Tasnimanam/A-Low-Cost-3D-Printed-Hand-Exoskeleton-with-Open-Source-Hardware-Licence/Hand Exoskeleton final model's CAD file/Hand ekoskeleton side view.jpg

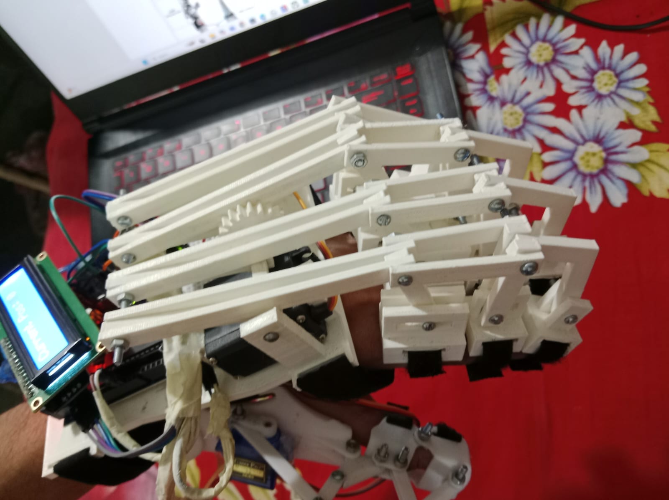
Hand Exoskeleton final model's CAD file/Hand ekoskeleton side view.jpg
