Tasnimanam/A-Low-Cost-3D-Printed-Hand-Exoskeleton-with-Open-Source-Hardware-Licence/Hand Exoskeleton final model's CAD file/little finger/2x LF arm 1.stl

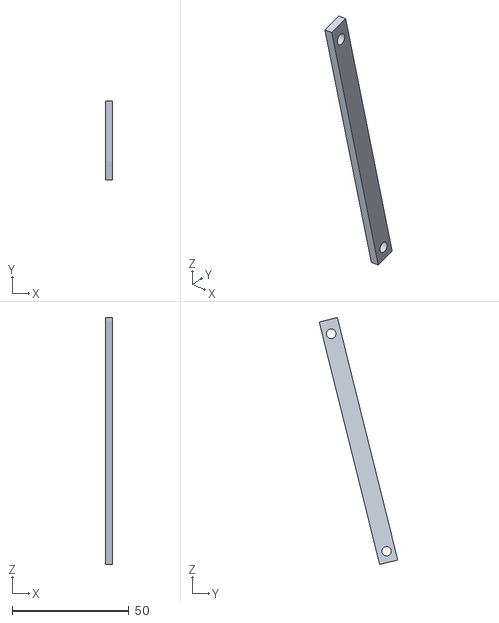
[picture p37: CAD file, 2026-04-23]
Hand Exoskeleton final model's CAD file/little finger/2x LF arm 1.stl
3.00 x 33.6 x 105.7
