Tasnimanam/A-Low-Cost-3D-Printed-Hand-Exoskeleton-with-Open-Source-Hardware-Licence/Hand Exoskeleton final model's CAD file/Ring finger/arm 2.stl

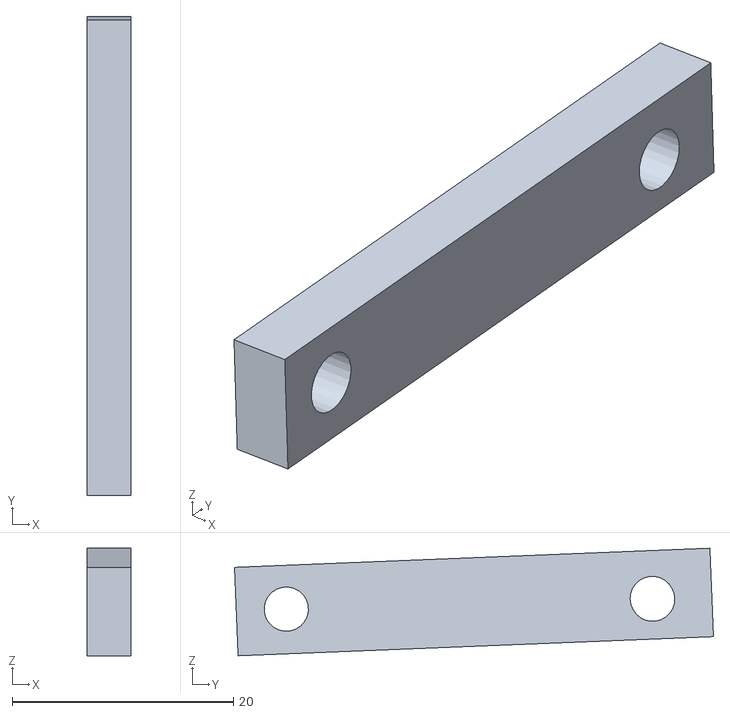
[picture p38: CAD file, 2026-04-23]
Hand Exoskeleton final model's CAD file/Ring finger/arm 2.stl
4.00 x 43.3 x 9.72
