Tasnimanam/A-Low-Cost-3D-Printed-Hand-Exoskeleton-with-Open-Source-Hardware-Licence/Hand Exoskeleton final model's CAD file/Index finger/2x arm 4.stl

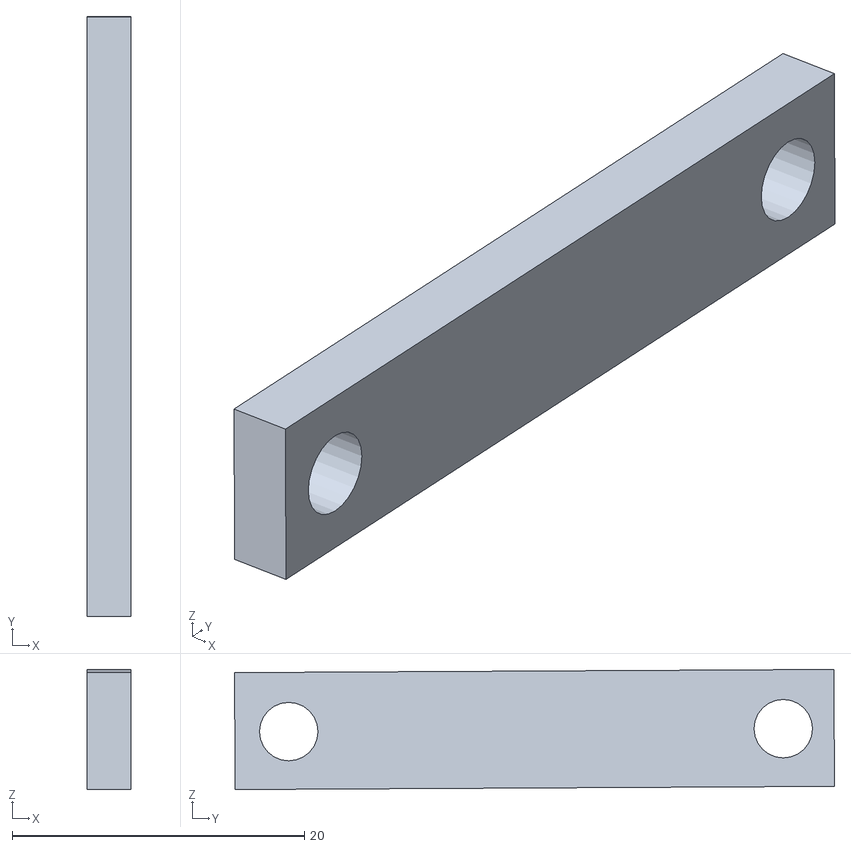
[picture p39: CAD file, 2026-04-23]
Hand Exoskeleton final model's CAD file/Index finger/2x arm 4.stl
3.00 x 41.0 x 8.22
