Tasnimanam/A-Low-Cost-3D-Printed-Hand-Exoskeleton-with-Open-Source-Hardware-Licence/Hand Exoskeleton final model's CAD file/Thumb/part 1.SLDPRT

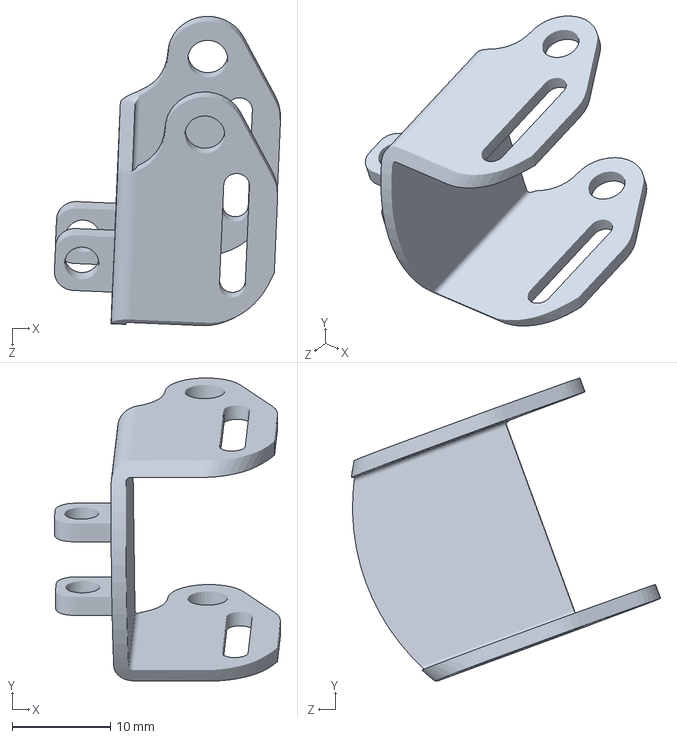
[picture p40: CAD file, 2026-04-23]
Hand Exoskeleton final model's CAD file/Thumb/part 1.SLDPRT
23.1 x 30.9 x 31.6 mm
