Tasnimanam/A-Low-Cost-3D-Printed-Hand-Exoskeleton-with-Open-Source-Hardware-Licence/Hand Exoskeleton final model's CAD file/little finger/2x LF arm 3.stl

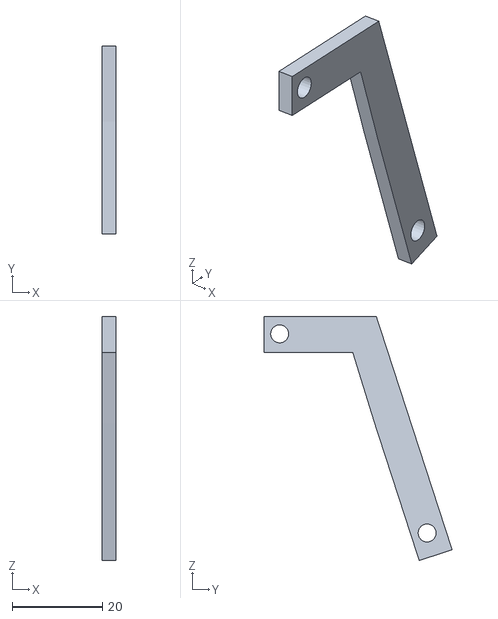
[picture p41: CAD file, 2026-04-23]
Hand Exoskeleton final model's CAD file/little finger/2x LF arm 3.stl
3.00 x 41.8 x 54.2
