Tasnimanam/A-Low-Cost-3D-Printed-Hand-Exoskeleton-with-Open-Source-Hardware-Licence/Hand Exoskeleton final model's CAD file/Middle finger/arm 5.stl

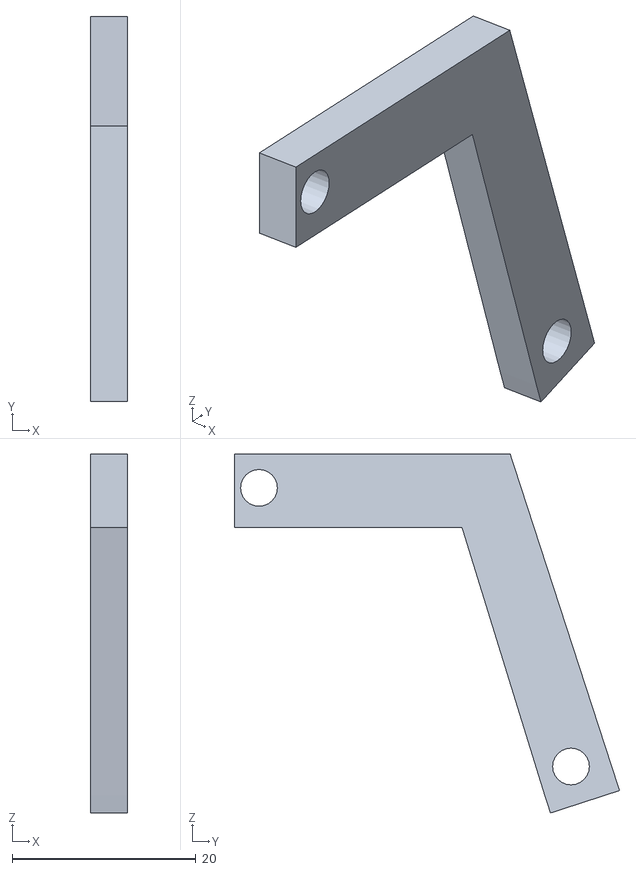
[picture p42: CAD file, 2026-04-23]
Hand Exoskeleton final model's CAD file/Middle finger/arm 5.stl
4.00 x 41.9 x 39.1
