Tasnimanam/A-Low-Cost-3D-Printed-Hand-Exoskeleton-with-Open-Source-Hardware-Licence/Hand Exoskeleton final model's CAD file/Thumb/part 5.STL

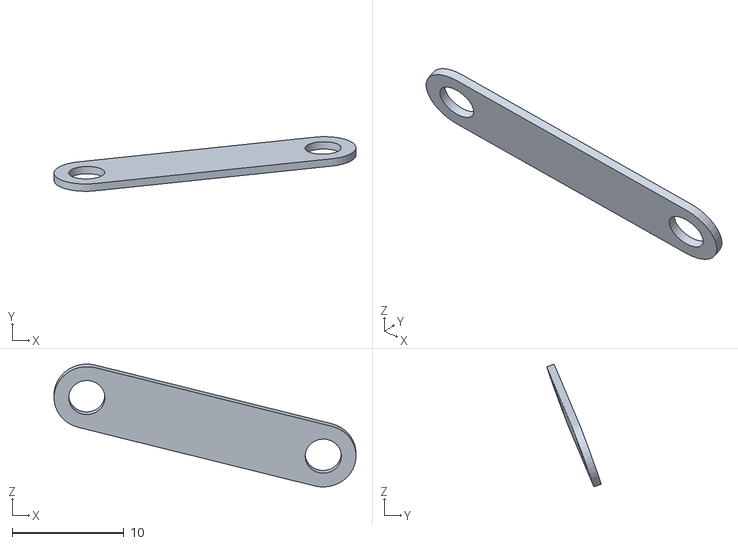
[picture p43: CAD file, 2026-04-23]
Hand Exoskeleton final model's CAD file/Thumb/part 5.STL
27.1 x 4.90 x 11.0
