Tasnimanam/A-Low-Cost-3D-Printed-Hand-Exoskeleton-with-Open-Source-Hardware-Licence/Hand Exoskeleton final model's CAD file/little finger/LF proximal phalanx support.stl

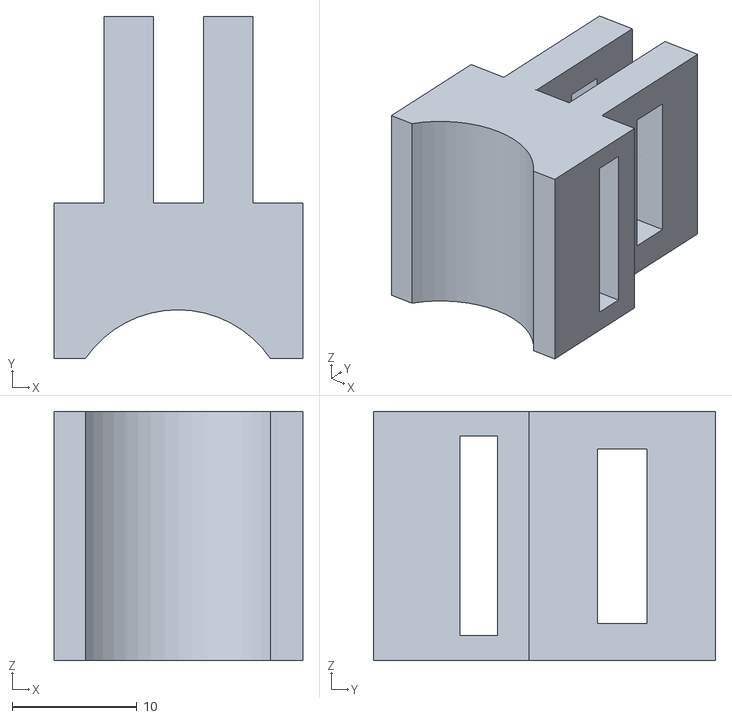
[picture p44: CAD file, 2026-04-23]
Hand Exoskeleton final model's CAD file/little finger/LF proximal phalanx support.stl
20.0 x 27.5 x 20.0
