Tasnimanam/A-Low-Cost-3D-Printed-Hand-Exoskeleton-with-Open-Source-Hardware-Licence/Hand Exoskeleton final model's CAD file/Thumb/part 8.SLDPRT

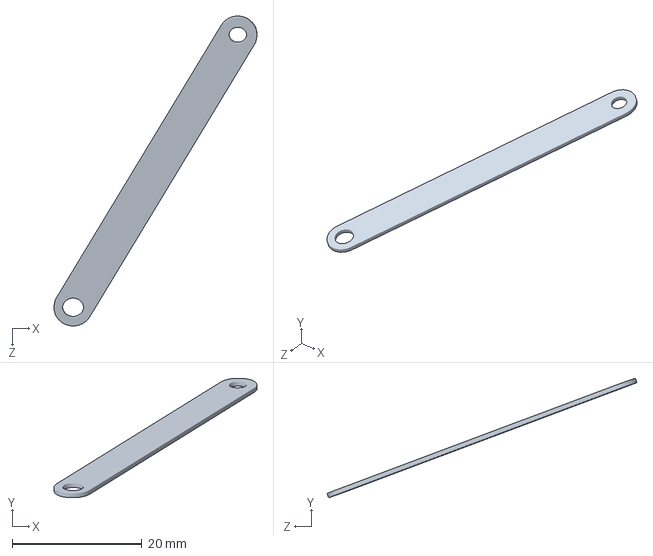
[picture p45: CAD file, 2026-04-23]
Hand Exoskeleton final model's CAD file/Thumb/part 8.SLDPRT
31.2 x 18.4 x 47.7 mm
