Tasnimanam/A-Low-Cost-3D-Printed-Hand-Exoskeleton-with-Open-Source-Hardware-Licence/Hand Exoskeleton final model's CAD file/Thumb/part 7.SLDPRT

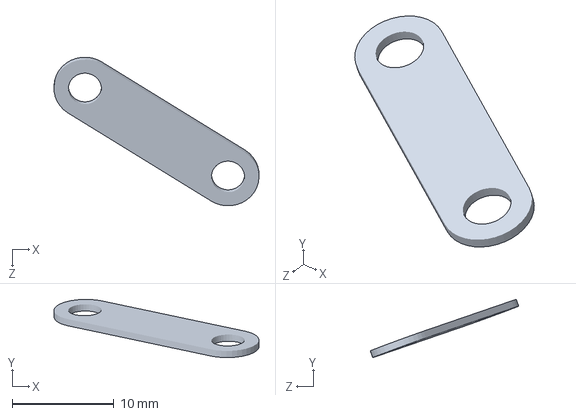
[picture p46: CAD file, 2026-04-23]
Hand Exoskeleton final model's CAD file/Thumb/part 7.SLDPRT
20.1 x 5.72 x 14.6 mm
