Tasnimanam/A-Low-Cost-3D-Printed-Hand-Exoskeleton-with-Open-Source-Hardware-Licence/Hand Exoskeleton final model's CAD file/Thumb/part 6.SLDPRT

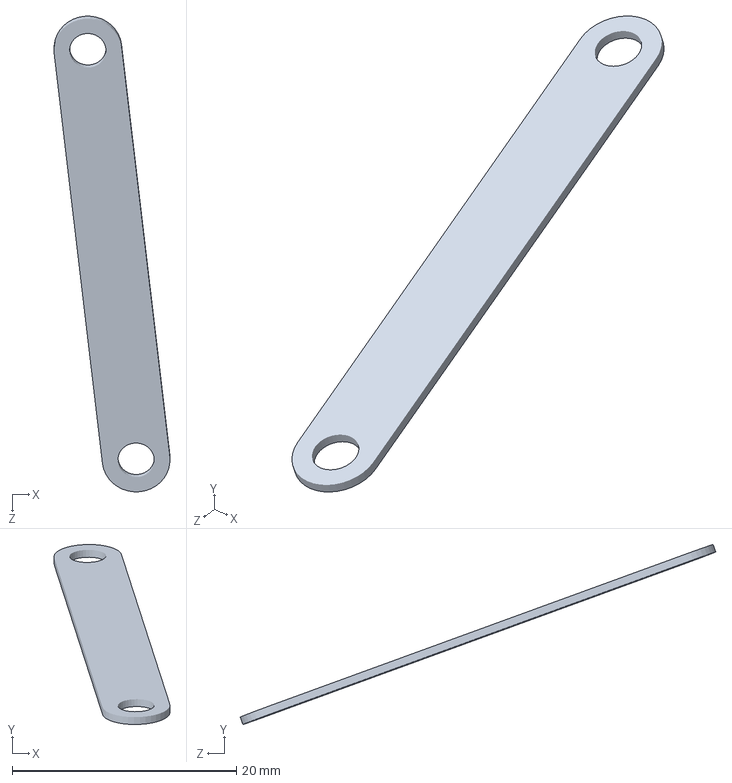
[picture p47: CAD file, 2026-04-23]
Hand Exoskeleton final model's CAD file/Thumb/part 6.SLDPRT
10.3 x 16.1 x 42.4 mm
