Tasnimanam/A-Low-Cost-3D-Printed-Hand-Exoskeleton-with-Open-Source-Hardware-Licence/Hand Exoskeleton final model's CAD file/Thumb/Thumb shaft.SLDPRT

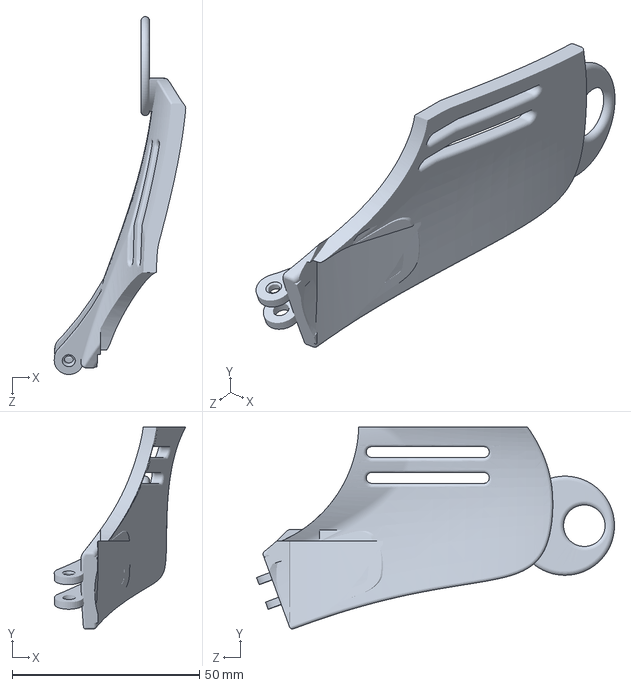
[picture p48: CAD file, 2026-04-23]
Hand Exoskeleton final model's CAD file/Thumb/Thumb shaft.SLDPRT
35.1 x 53.9 x 95.5 mm
