Tasnimanam/A-Low-Cost-3D-Printed-Hand-Exoskeleton-with-Open-Source-Hardware-Licence/Hand Exoskeleton final model's CAD file/Thumb/part 2.SLDPRT

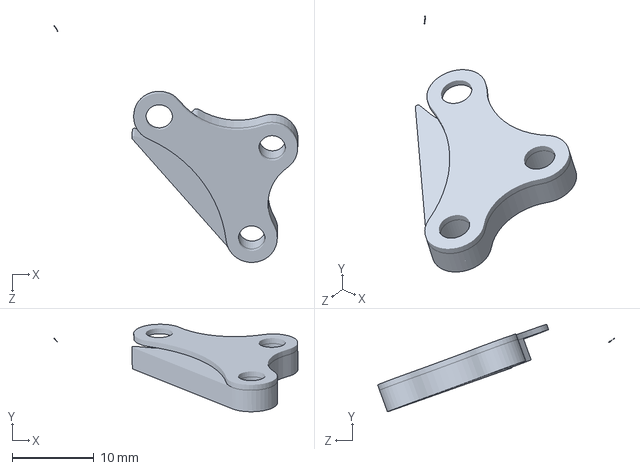
[picture p49: CAD file, 2026-04-23]
Hand Exoskeleton final model's CAD file/Thumb/part 2.SLDPRT
29.8 x 10.7 x 28.9 mm
