Tasnimanam/A-Low-Cost-3D-Printed-Hand-Exoskeleton-with-Open-Source-Hardware-Licence/Hand Exoskeleton final model's CAD file/Assembly of full model in SOLIDWORKS.jpg

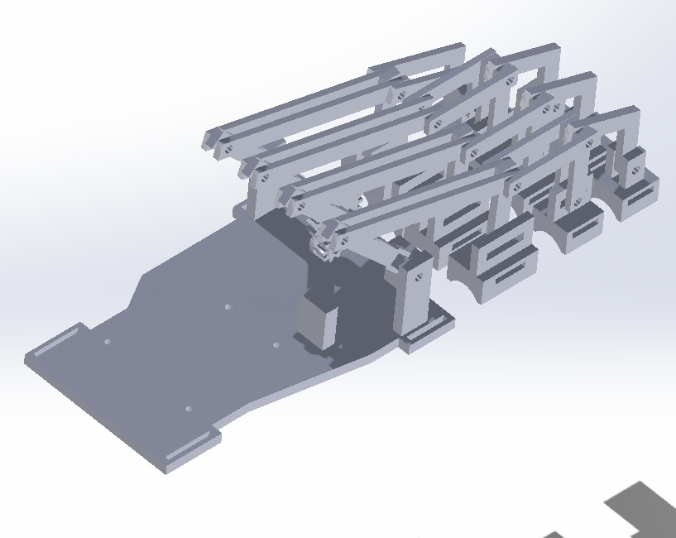
Hand Exoskeleton final model's CAD file/Assembly of full model in SOLIDWORKS.jpg
